BamdadKh/ArduinoLightsaber/firmware/lightsaber/sound_lengths.h

// Written by firmware/tools/build_sd_card.py. Lengths in ms of the main-channel tracks.
#pragma once
#define SND_IGNITE_MS 1450
#define SND_RETRACT_MS 721
#define SND_LENGTHS_MS {0, 1240, 12937, 1400, 671, 28784, 40, 160, 160, 480}  // index = track number
